heidepiek/Retro_Clock_2/Images/Back_of_Rear_Cover.jpg

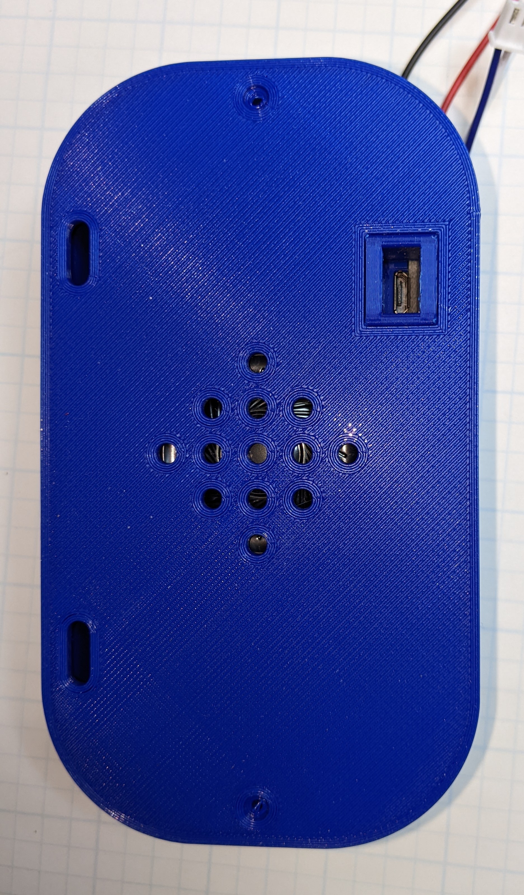
Images/Back_of_Rear_Cover.jpg
