heidepiek/Retro_Clock_2/Images/Bezel&Decal.jpg

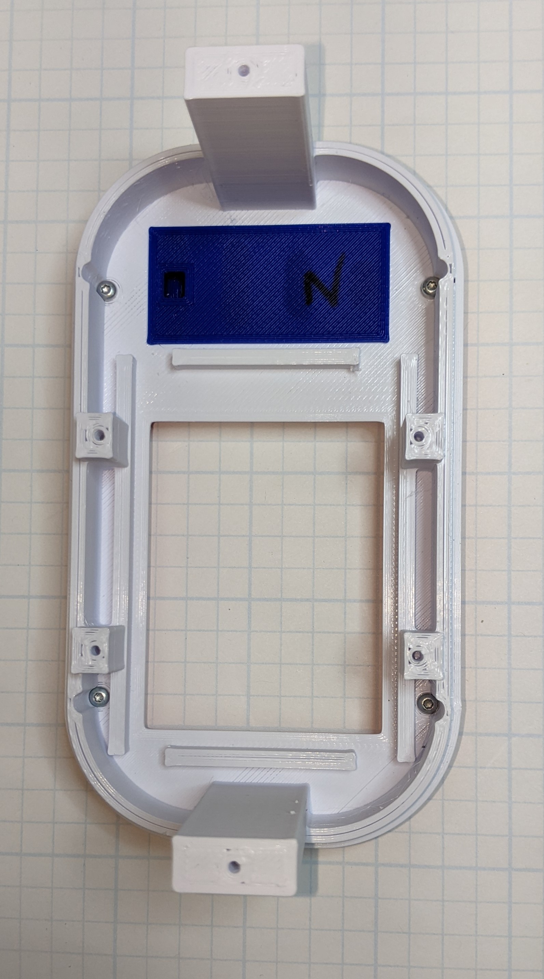
Images/Bezel&Decal.jpg
