heidepiek/Retro_Clock_2/Images/Bezel.jpg

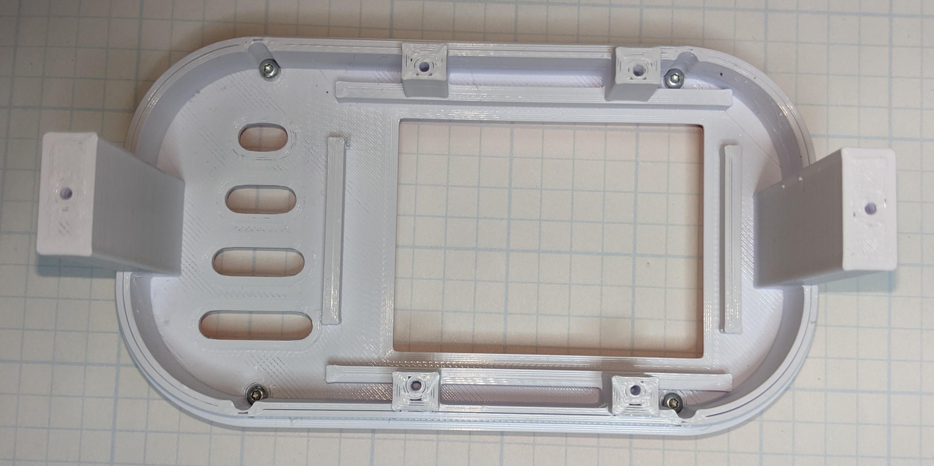
Images/Bezel.jpg
