heidepiek/Retro_Clock_2/Images/Bezel_&_Trim.jpg

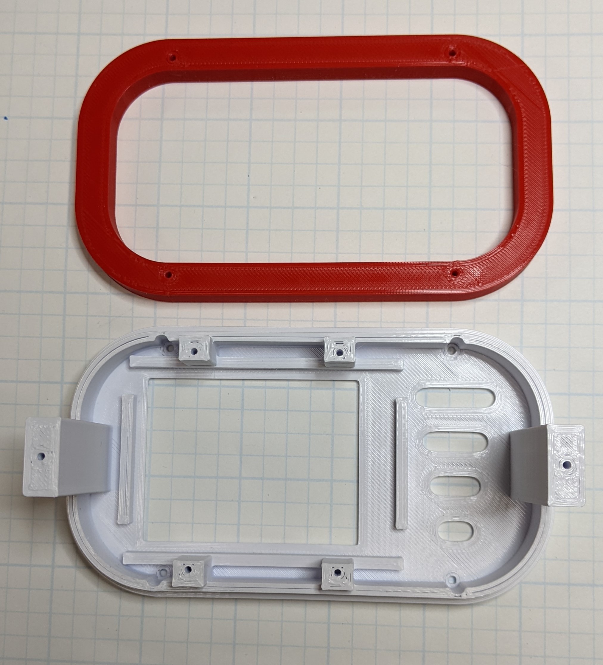
Images/Bezel_&_Trim.jpg
