heidepiek/Retro_Clock_2/Images/Bezel_Assy_&_Rear_Cover.jpg

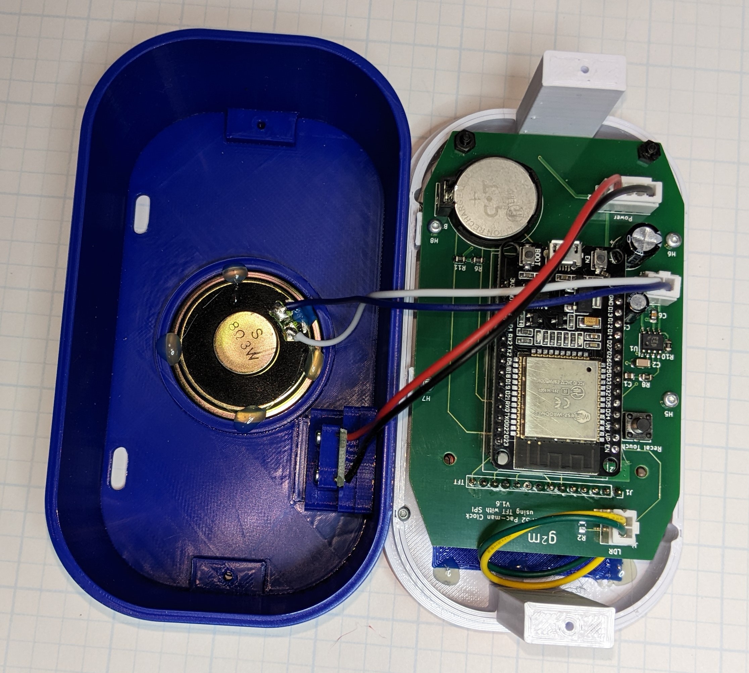
Images/Bezel_Assy_&_Rear_Cover.jpg
