heidepiek/Retro_Clock_2/Images/Bezel_with PCB_Assy.jpg

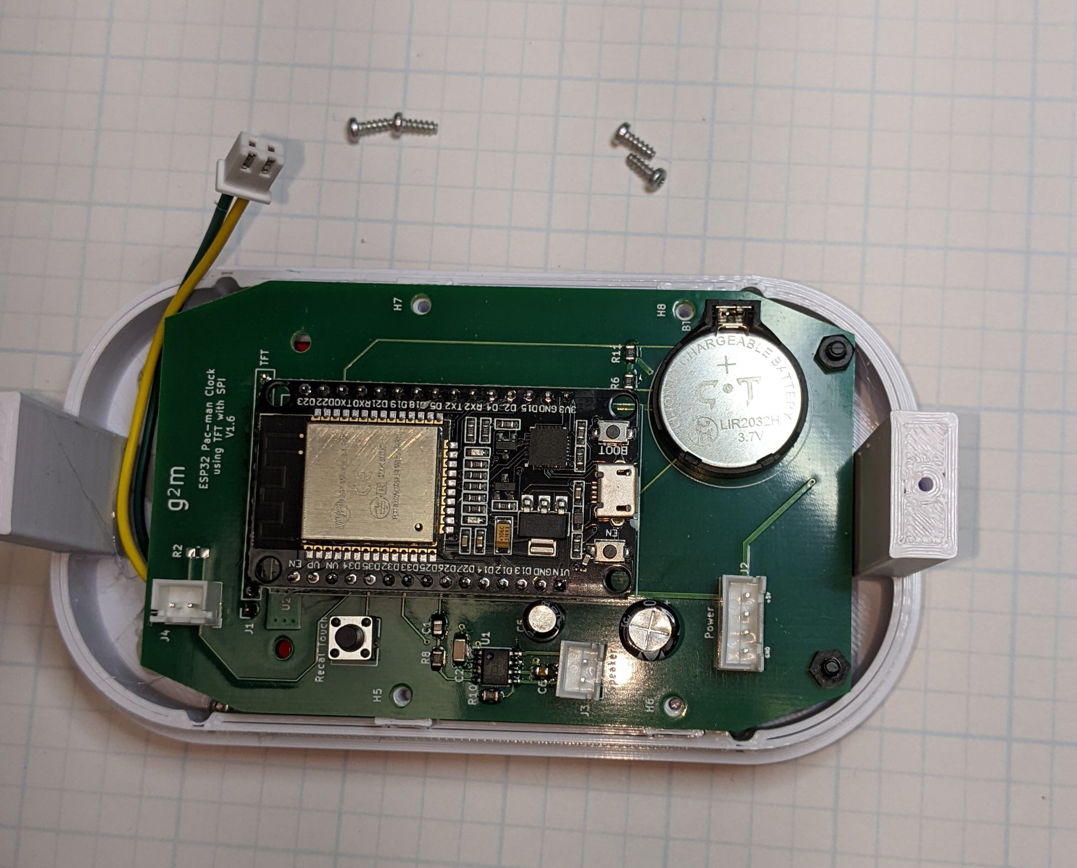
Images/Bezel_with PCB_Assy.jpg
