heidepiek/Retro_Clock_2/Images/Bezel_with_PCB_2.jpg

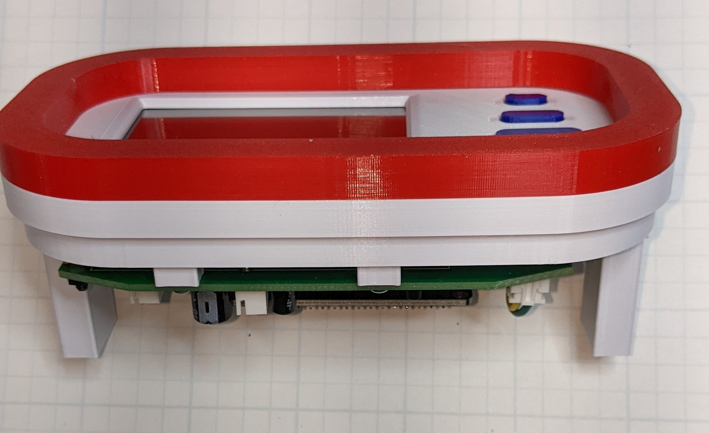
Images/Bezel_with_PCB_2.jpg
