heidepiek/Retro_Clock_2/Images/Decal&Bezel_Hotglue.jpg

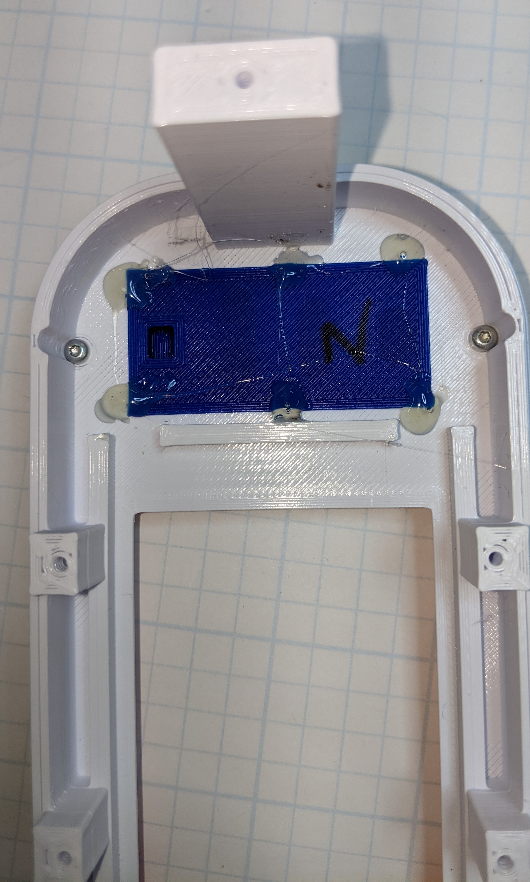
Images/Decal&Bezel_Hotglue.jpg
