heidepiek/Retro_Clock_2/Images/Decal.jpg

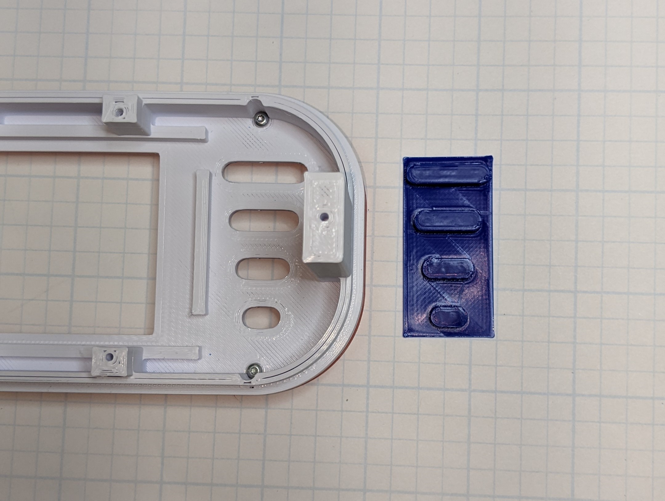
Images/Decal.jpg
