heidepiek/Retro_Clock_2/Images/Decal_with_LDR.jpg

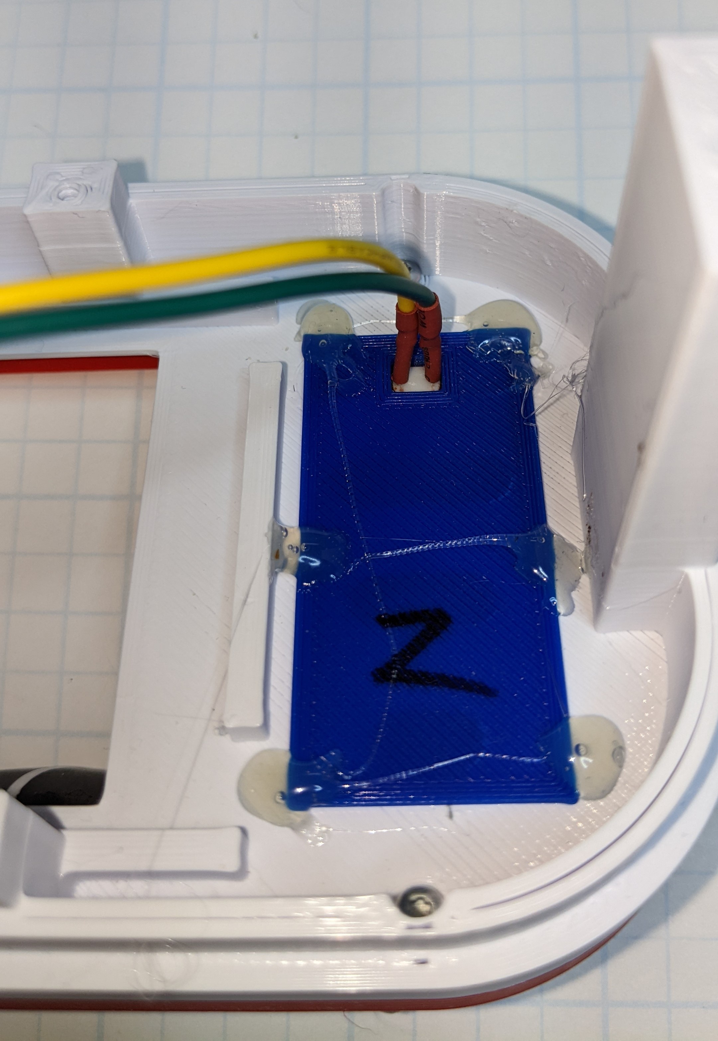
Images/Decal_with_LDR.jpg
