heidepiek/Retro_Clock_2/Images/LDR_Assy.jpg

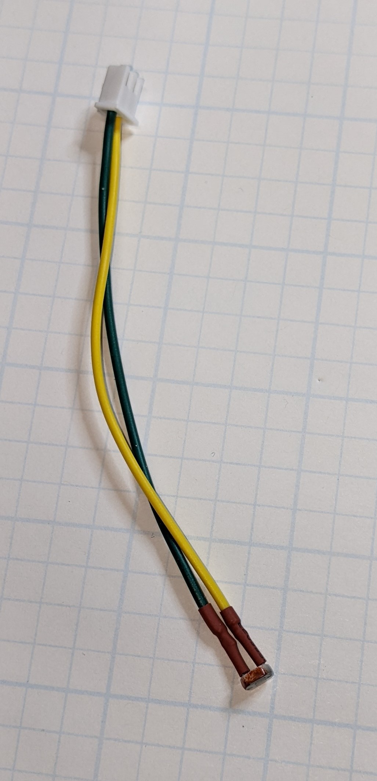
Images/LDR_Assy.jpg
