heidepiek/Retro_Clock_2/Images/LDR_Connected_to_PCB_Assy.jpg

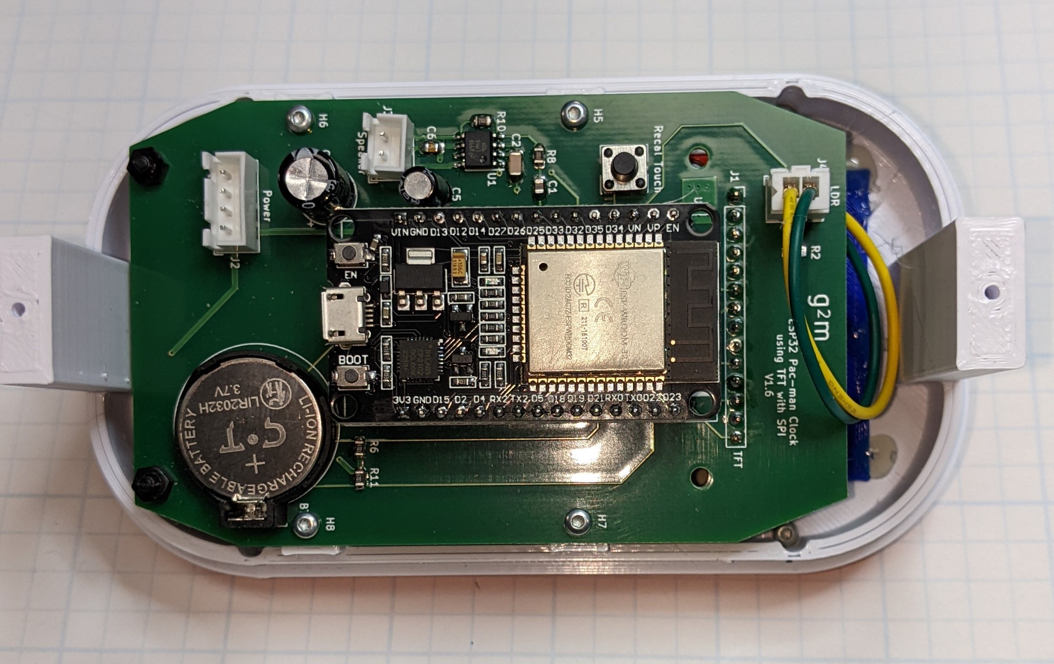
Images/LDR_Connected_to_PCB_Assy.jpg
