heidepiek/Retro_Clock_2/Images/LDR_Hotglued.jpg

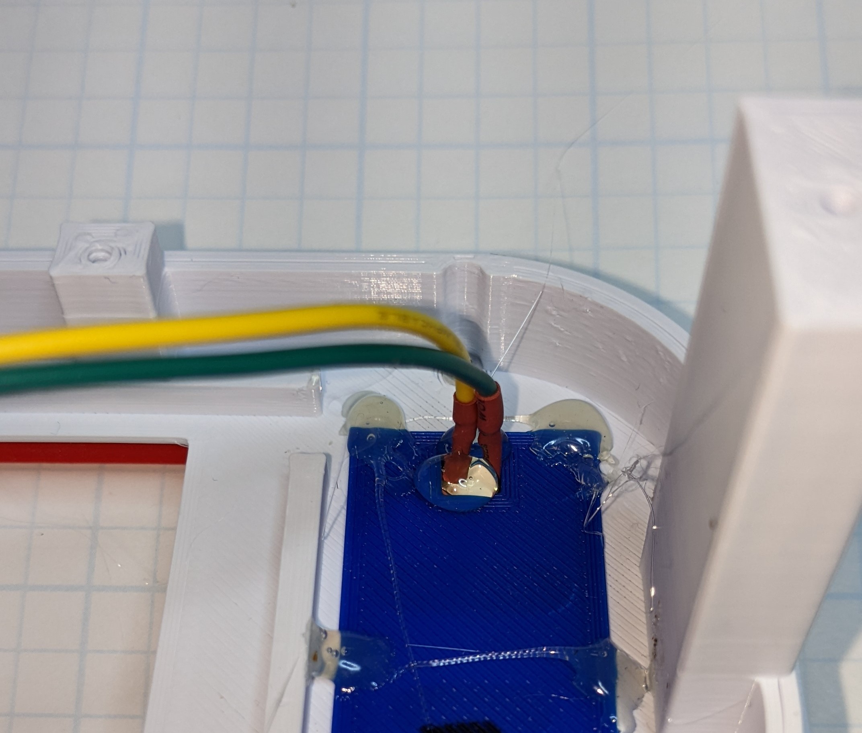
Images/LDR_Hotglued.jpg
