heidepiek/Retro_Clock_2/Images/PCB_&_Processor.jpg

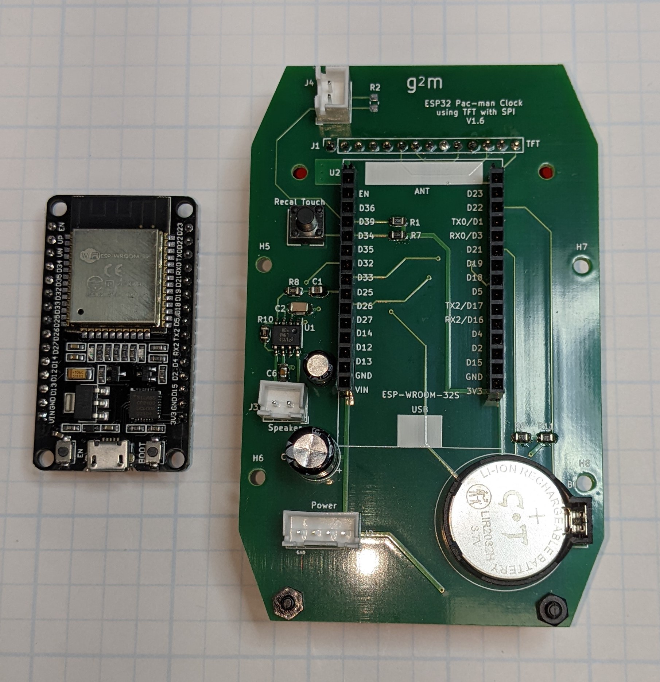
Images/PCB_&_Processor.jpg
