heidepiek/Retro_Clock_2/Images/PCB_Assy_Mounted_in_Bezel.jpg

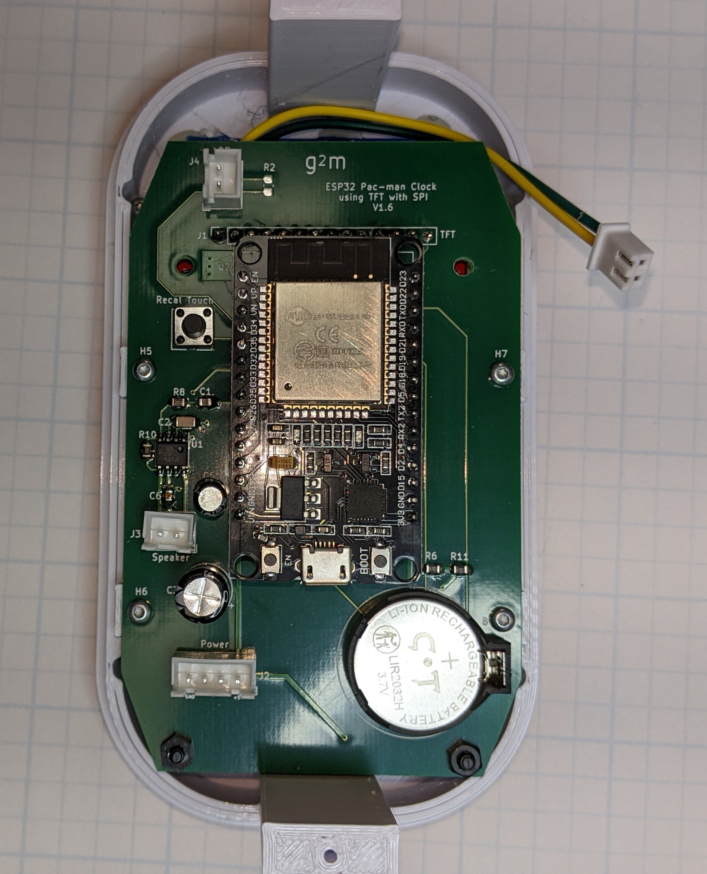
Images/PCB_Assy_Mounted_in_Bezel.jpg
