heidepiek/Retro_Clock_2/Images/PCB_Bottom.jpg

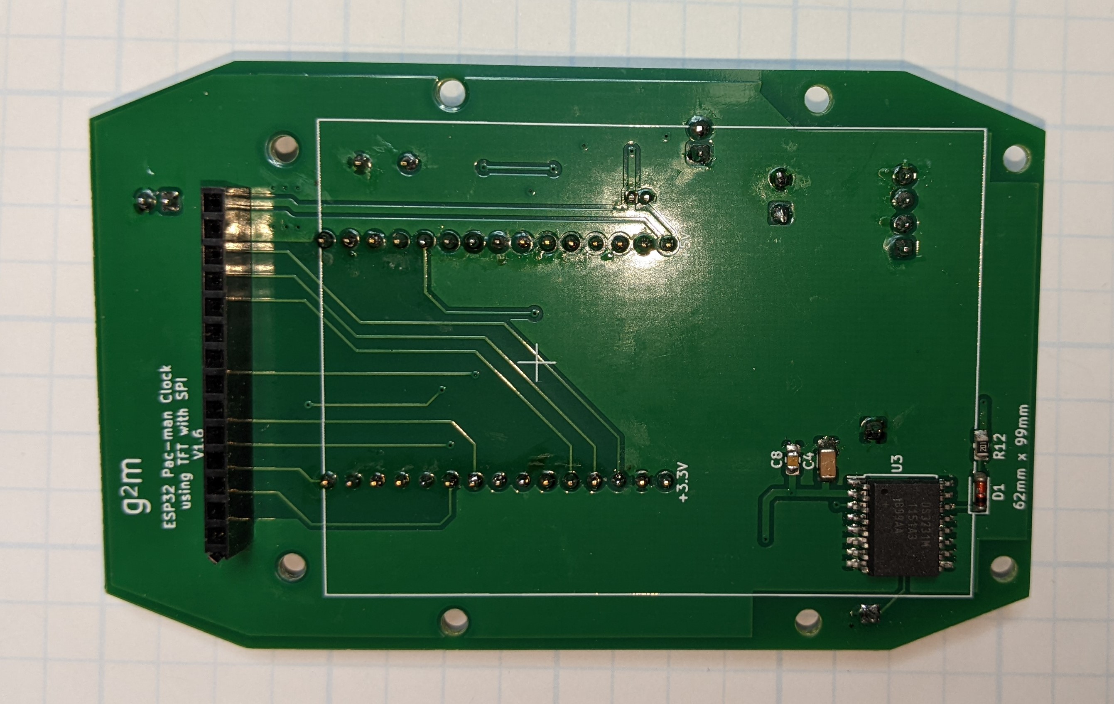
Images/PCB_Bottom.jpg
