heidepiek/Retro_Clock_2/Images/PCB_Top.jpg

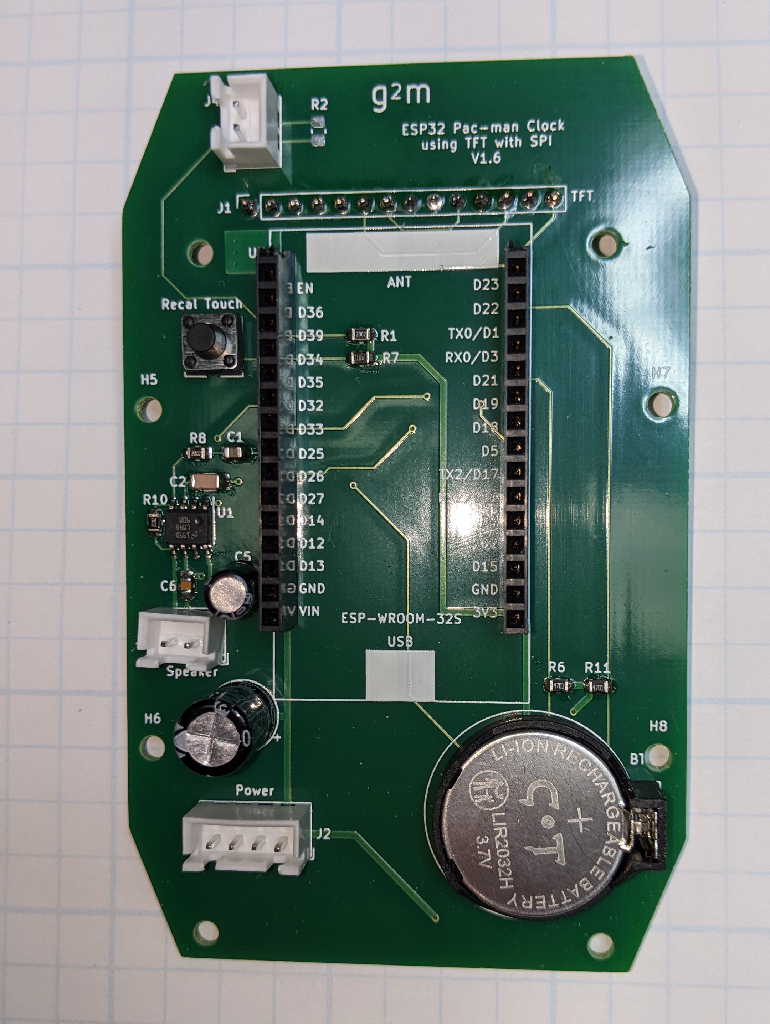
Images/PCB_Top.jpg
