heidepiek/Retro_Clock_2/Images/PCB_with_Processor.jpg

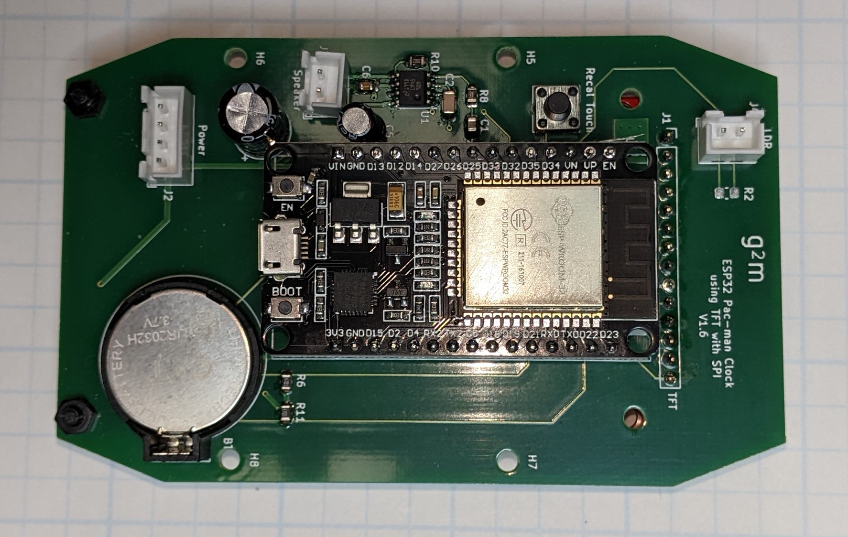
Images/PCB_with_Processor.jpg
