heidepiek/Retro_Clock_2/Images/Rear_Cover_&_USB_Assy.jpg

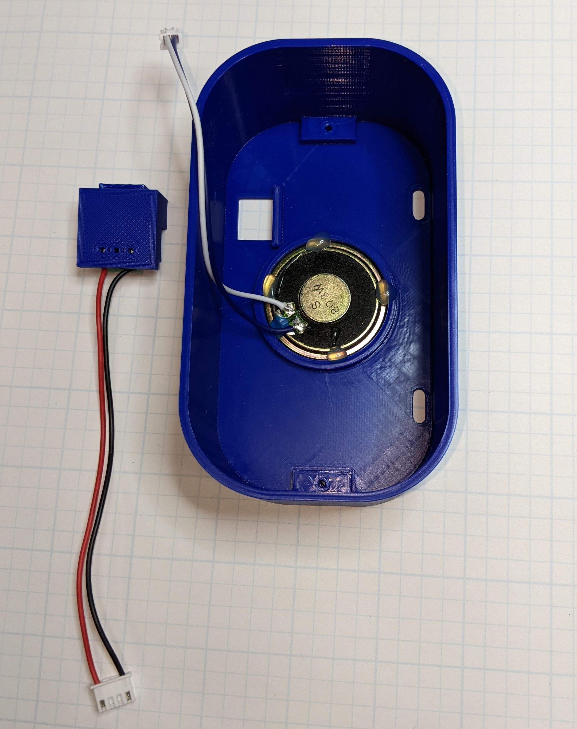
Images/Rear_Cover_&_USB_Assy.jpg
