heidepiek/Retro_Clock_2/Images/Rear_Cover_Screws.jpg

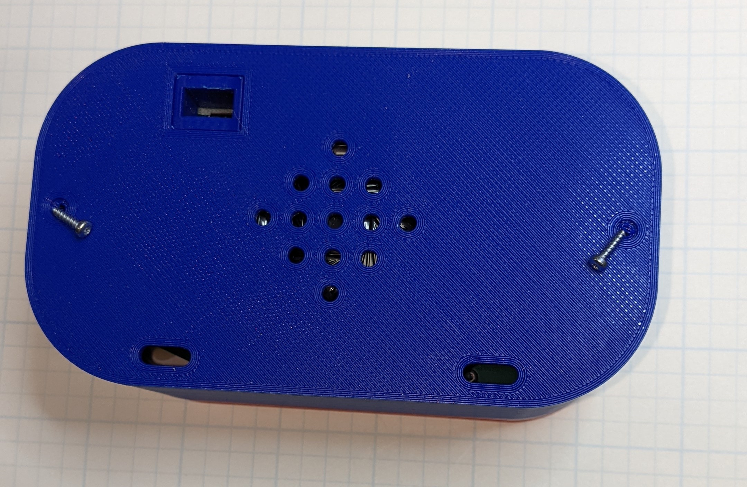
Images/Rear_Cover_Screws.jpg
