heidepiek/Retro_Clock_2/Images/RearCover & Speaker.jpg

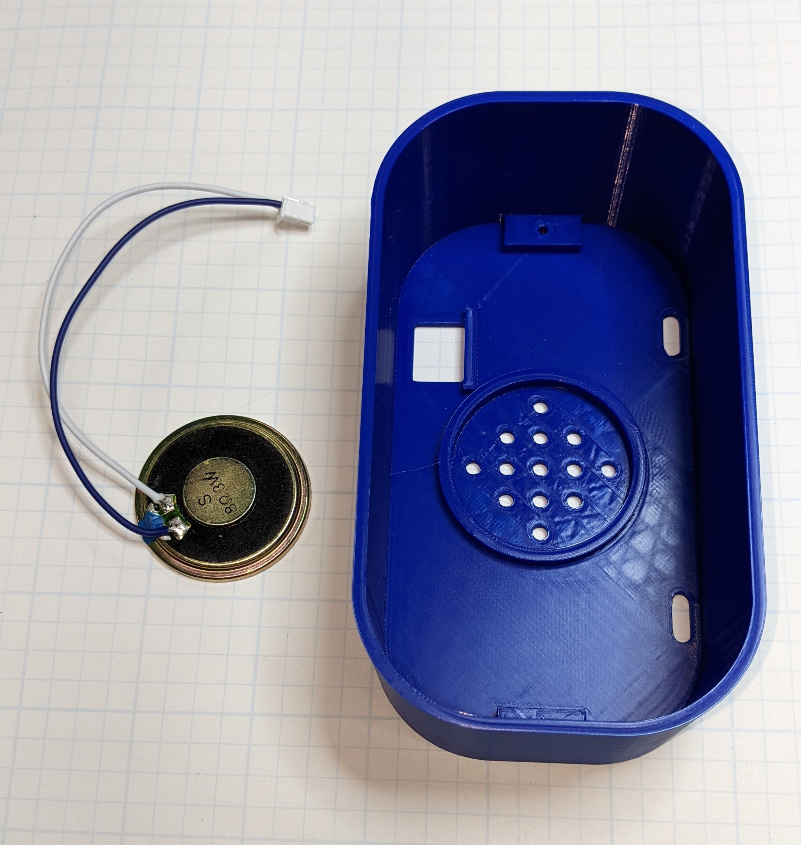
Images/RearCover & Speaker.jpg
