heidepiek/Retro_Clock_2/Images/Retro_Clock_Face.jpg

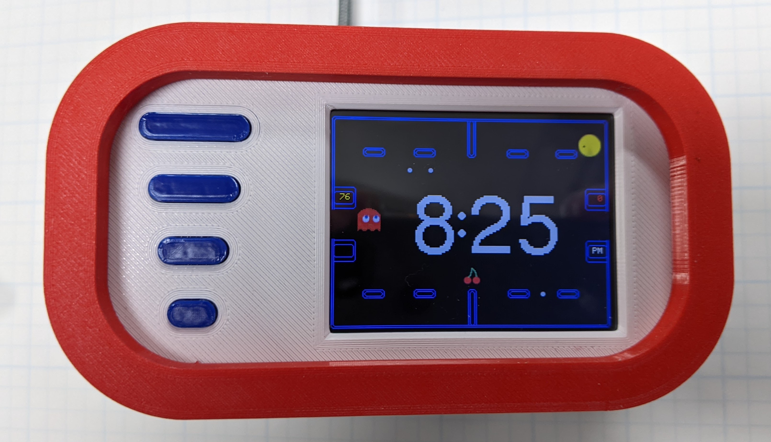
Images/Retro_Clock_Face.jpg
