heidepiek/Retro_Clock_2/Images/Speaker.jpg

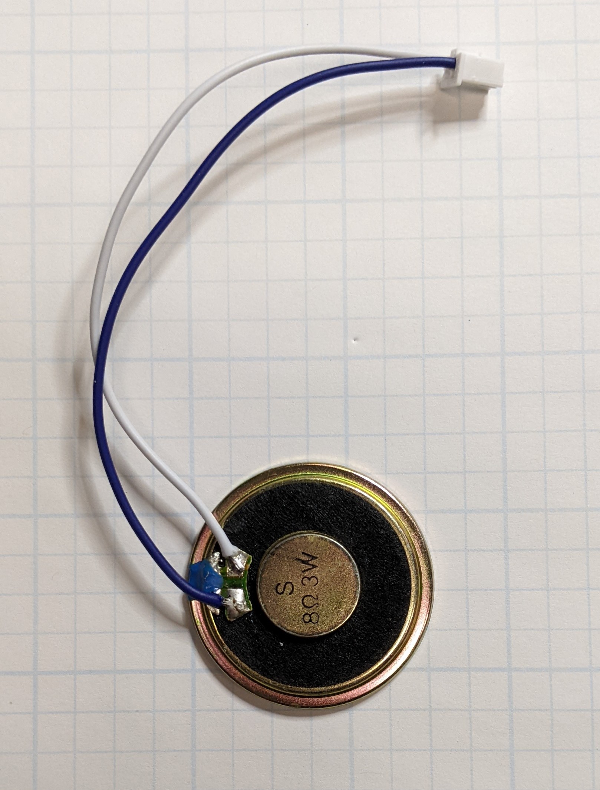
Images/Speaker.jpg
