heidepiek/Retro_Clock_2/Images/Speaker_Hotglued.jpg

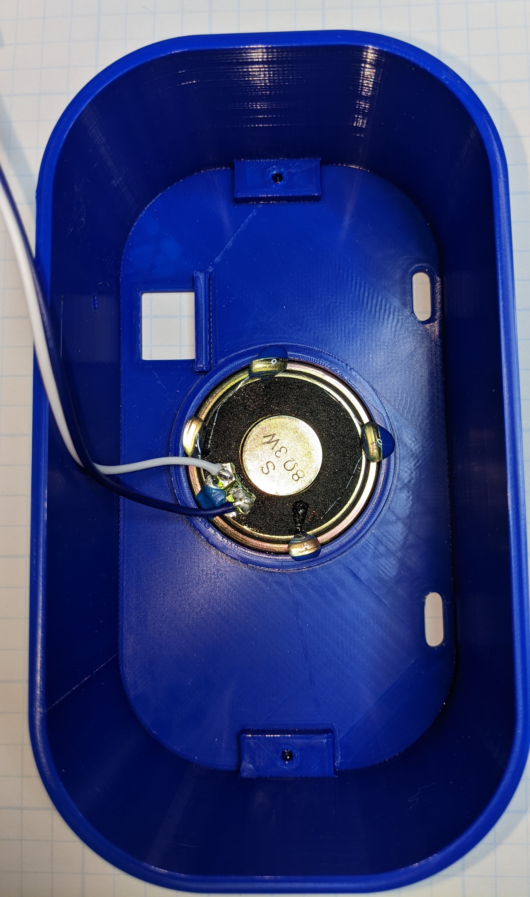
Images/Speaker_Hotglued.jpg
