heidepiek/Retro_Clock_2/Images/Speaker_in_Rear_Cover.jpg

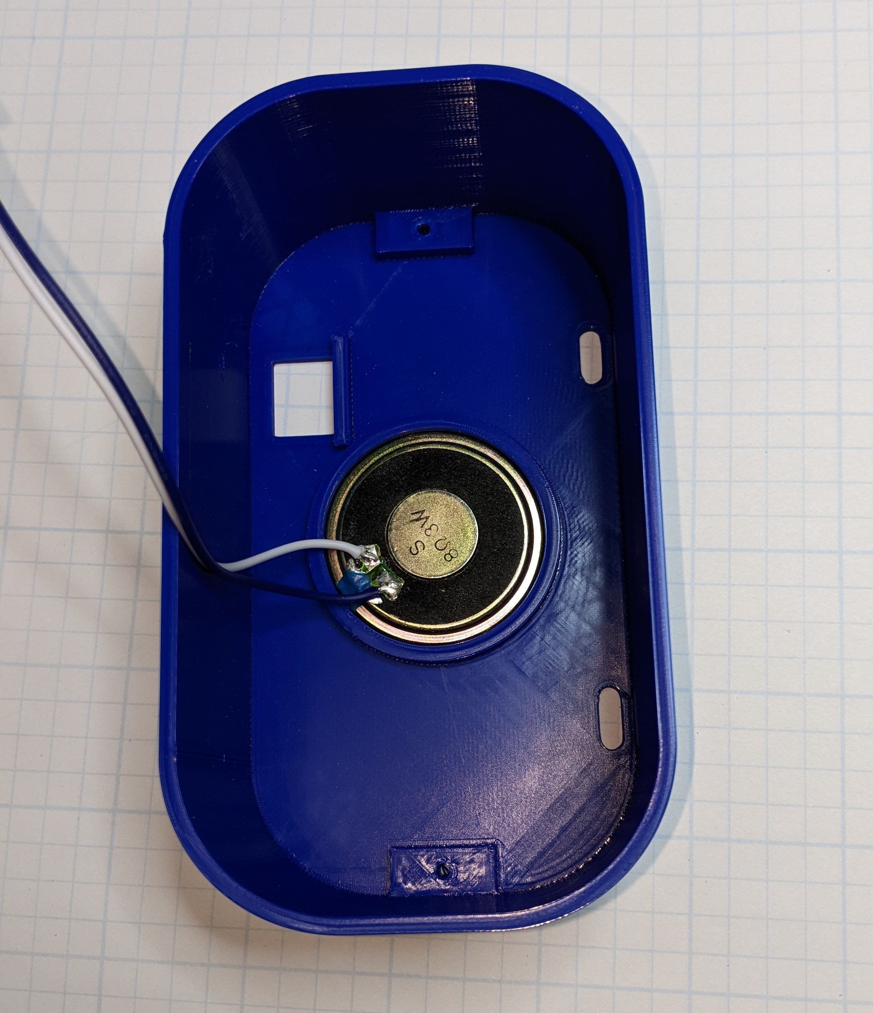
Images/Speaker_in_Rear_Cover.jpg
