heidepiek/Retro_Clock_2/Images/TFT_with_Standoffs.jpg

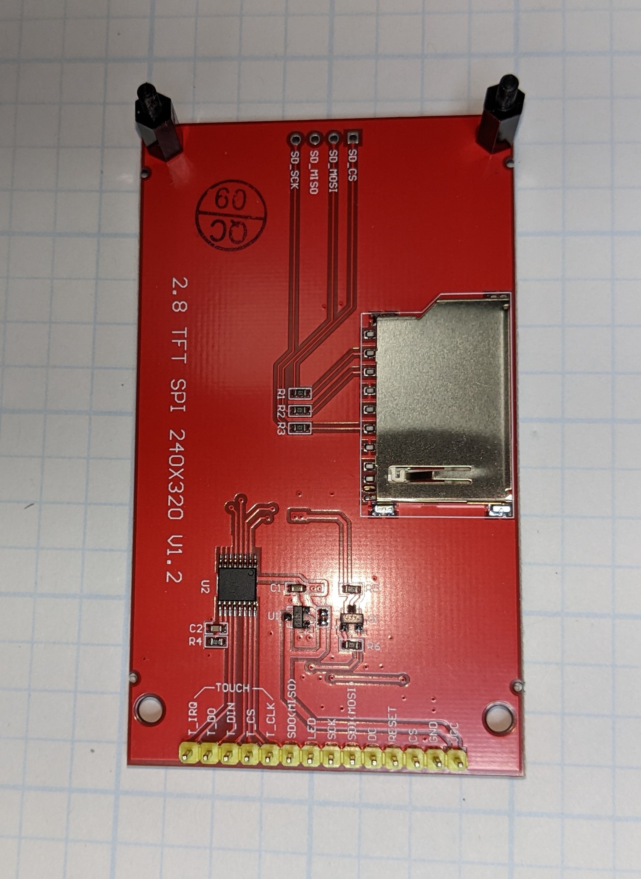
Images/TFT_with_Standoffs.jpg
