heidepiek/Retro_Clock_2/Images/USB_Bracket.jpg

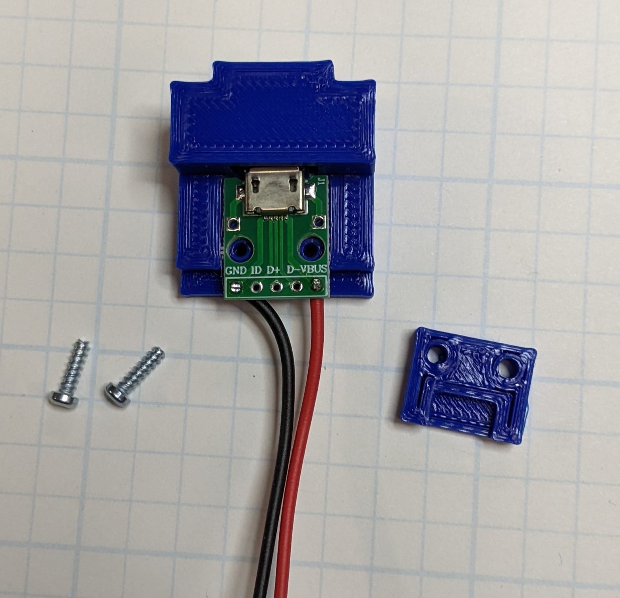
Images/USB_Bracket.jpg
