heidepiek/Retro_Clock_2/Images/USB_Bracket_Assy.jpg

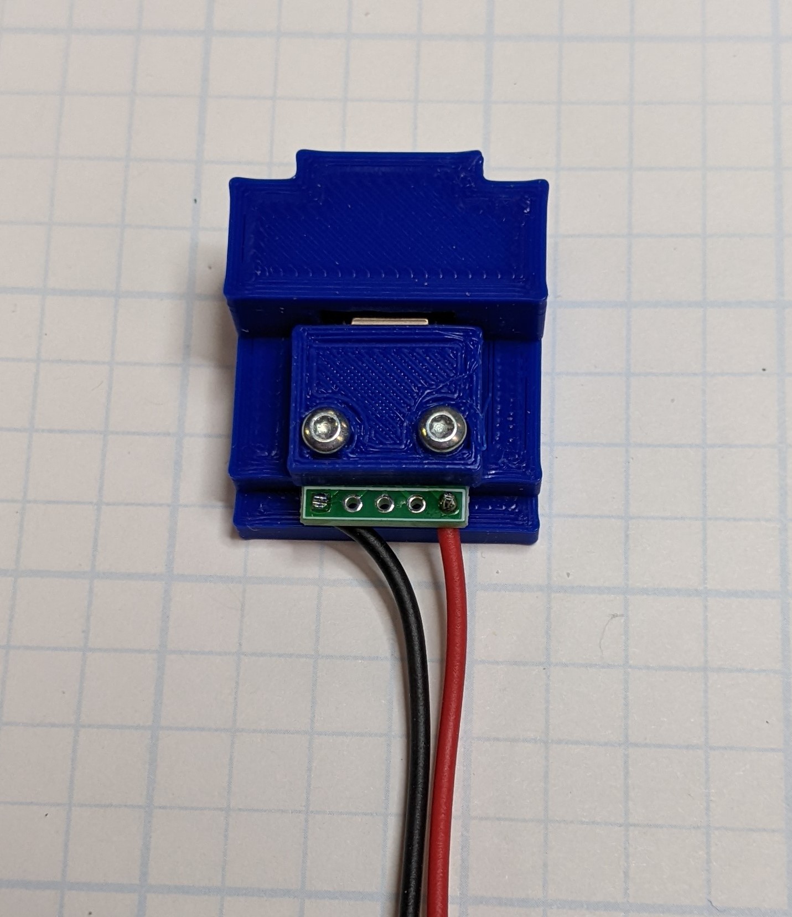
Images/USB_Bracket_Assy.jpg
