heidepiek/Retro_Clock_2/Images/USB_Securred.jpg

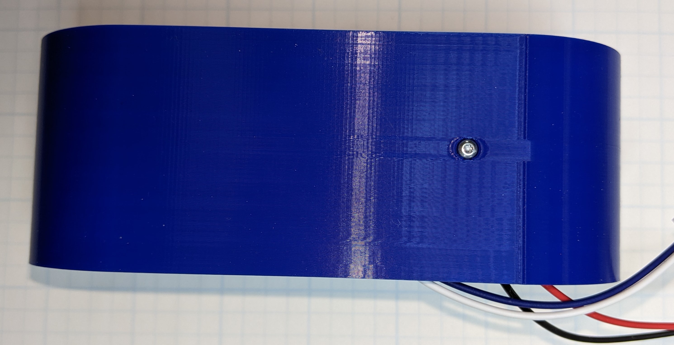
Images/USB_Securred.jpg
