heidepiek/Retro_Clock_2/Images/Assembled_Bezel&Trim.jpg

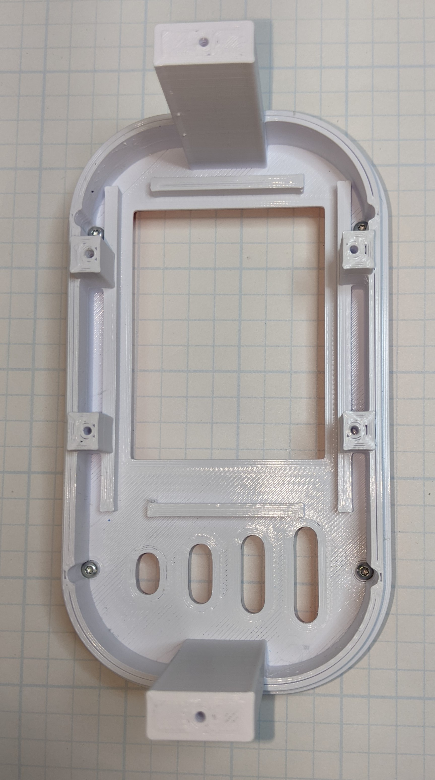
Images/Assembled_Bezel&Trim.jpg
