heidepiek/Retro_Clock_2/Images/Clock_with_Feet_Installed.jpg

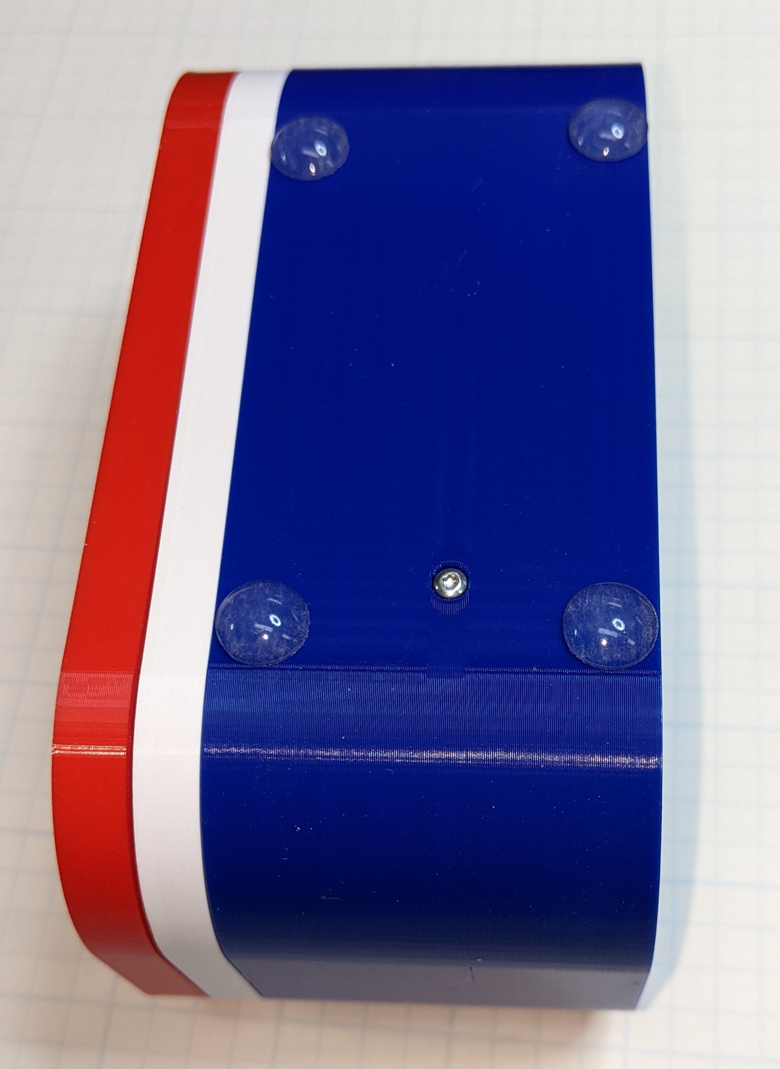
Images/Clock_with_Feet_Installed.jpg
