heidepiek/Retro_Clock_2/Images/PCB_TFT_Assembly.jpg

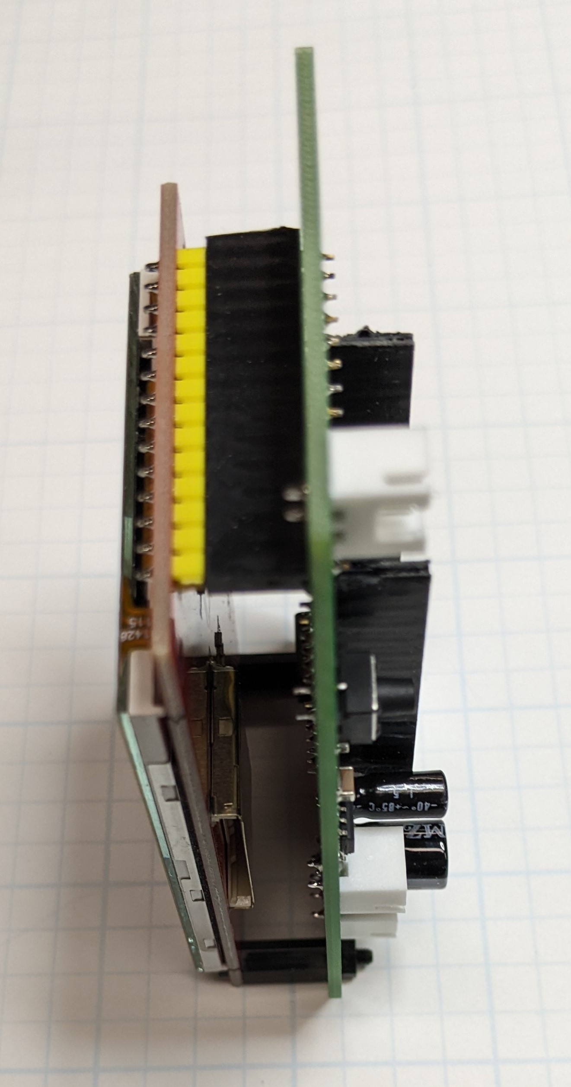
Images/PCB_TFT_Assembly.jpg
