heidepiek/Retro_Clock_2/Images/Rear_Cover_with_USB_Installed.jpg

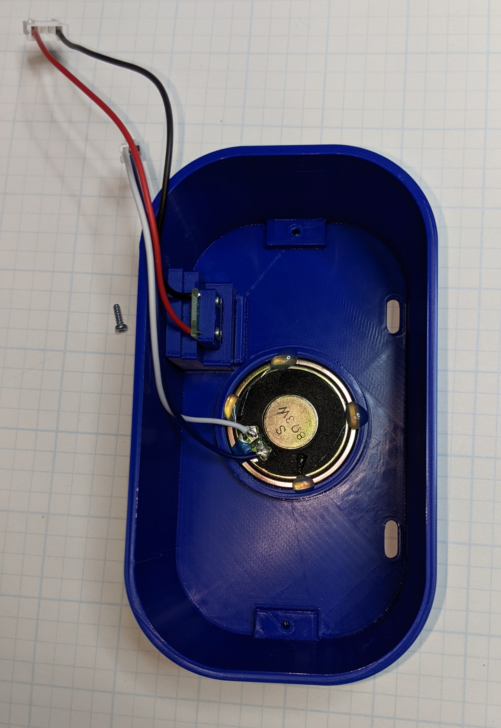
Images/Rear_Cover_with_USB_Installed.jpg
