heidepiek/Retro_Clock_2/src/SoundData.h

// sound in WAV format, we're not concerned with most of the header bytes
// just samples per second and data size, we will always save in 8bit 
// unsigned pcm
// sample rate is at offset 24 (4 bytes), data size at offset 4 (4bytes)
//
//  PlayingTime = 4307.5 milliseconds (approx 4.3 seconds)

#ifdef BUFFERED_WAV
//
//  When using BUFFERED_WAV, the pacman and gobble WAV data occupy the same buffer
//  to save on memory. The pacman WAV starts at offset 0 and the gobble WAV starts 
//  at offset 48 so that both the pacman and gobble WAV headers are in memory when 
//  the Pacman and pacmangobble objects are created.
//  Whenever a request is made to play either WAV the code knows
//  which WAV is occupying the buffer and if not the requested WAV it will
//  load the desired WAV from SPIFFS. 
//  The gobble WAV is about half the size of the pacman WAV.
//
//  size = 34468
//
unsigned char PROGMEM PM[35000] = {
  //  pacman WAV header
  0x52, 0x49, 0x46, 0x46, 0x9C, 0x86, 0x00, 0x00, 0x57, 0x41, 0x56, 0x45,   // size[7:4} = 0x0000869C (34460)
  0x66, 0x6D, 0x74, 0x20, 0x10, 0x00, 0x00, 0x00, 0x01, 0x00, 0x01, 0x00,   // FMT chunk ID[15:12] = 0x20746D66
  0x40, 0x1F, 0x00, 0x00, 0x40, 0x1F, 0x00, 0x00, 0x01, 0x00, 0x08, 0x00,   // sample rate[27:24] 0x00001F40 (8000)
  0x64, 0x61, 0x74, 0x61, 0x13, 0x86, 0x00, 0x00, 0x80, 0x7F, 0x7F, 0x7F,   // Data start
  // gobble WAV header
  0x52, 0x49, 0x46, 0x46, 0x5A, 0x3E, 0x00, 0x00, 0x57, 0x41, 0x56, 0x45,   // size[7:4] = 0x00003E5A (15962)
  0x66, 0x6D, 0x74, 0x20, 0x10, 0x00, 0x00, 0x00, 0x01, 0x00, 0x01, 0x00,   // FMT chunk ID[15:12] = 0x20746D66
  0x22, 0x56, 0x00, 0x00, 0x22, 0x56, 0x00, 0x00, 0x01, 0x00, 0x08, 0x00,   // sample rate[27:24] = 0x00005622 (22050)
  0x64, 0x61, 0x74, 0x61, 0xB8, 0x3D, 0x00, 0x00, 0x81, 0x82, 0x80, 0x80,   // Data start
};

#else
unsigned char PROGMEM PM[34468] = {
  0x52, 0x49, 0x46, 0x46, 0x9C, 0x86, 0x00, 0x00, 0x57, 0x41, 0x56, 0x45,   // size[7:4} = 0x0000869C (34460)
  0x66, 0x6D, 0x74, 0x20, 0x10, 0x00, 0x00, 0x00, 0x01, 0x00, 0x01, 0x00,   // FMT chunk ID[15:12] = 0x20746D66
  0x40, 0x1F, 0x00, 0x00, 0x40, 0x1F, 0x00, 0x00, 0x01, 0x00, 0x08, 0x00,   // sample rate[27:24] 0x00001F40 (8000)
  0x64, 0x61, 0x74, 0x61, 0x13, 0x86, 0x00, 0x00, 0x80, 0x7F, 0x7F, 0x7F,   // Data start 
  0x7F, 0x7F, 0x7F, 0x7F, 0x7F, 0x7F, 0x7F, 0x7F, 0x7F, 0x7F, 0x7F, 0x7F,
  0x7F, 0x7F, 0x7F, 0x7F, 0x7F, 0x7F, 0x7F, 0x7F, 0x7F, 0x7F, 0x7F, 0x7F,
  0x7F, 0x7F, 0x7F, 0x7F, 0x7F, 0x7F, 0x7F, 0x7F, 0x7F, 0x7F, 0x7F, 0x7F,
  0x7F, 0x7F, 0x7F, 0x7F, 0x7F, 0x7F, 0x7F, 0x7F, 0x7F, 0x7F, 0x7F, 0x7F,
  0x7F, 0x7F, 0x7F, 0x7F, 0x7F, 0x7F, 0x7F, 0x7F, 0x7F, 0x7F, 0x7F, 0x7F,
  0x7F, 0x7F, 0x7F, 0x7F, 0x7F, 0x7F, 0x7F, 0x7F, 0x80, 0x7F, 0x7F, 0x7F,
  0x7F, 0x7F, 0x7F, 0x7F, 0x7F, 0x7F, 0x7F, 0x80, 0x7F, 0x7F, 0x7F, 0x7F,
  0x7F, 0x7F, 0x7F, 0x7F, 0x7F, 0x7F, 0x7F, 0x7F, 0x7F, 0x7F, 0x7F, 0x7F,
  0x7F, 0x7F, 0x7F, 0x7F, 0x7F, 0x7F, 0x7F, 0x7F, 0x7F, 0x7F, 0x7F, 0x7F,
  0x7F, 0x7F, 0x7F, 0x7F, 0x7F, 0x7F, 0x7F, 0x7F, 0x7F, 0x7F, 0x7F, 0x7F,
  0x7F, 0x7F, 0x7F, 0x7F, 0x7F, 0x7F, 0x7F, 0x7F, 0x7F, 0x7F, 0x7F, 0x7F,
  0x7F, 0x7F, 0x7F, 0x7F, 0x7F, 0x7F, 0x7F, 0x7F, 0x7F, 0x7F, 0x7F, 0x7F,
  0x80, 0x7F, 0x7F, 0x7F, 0x7F, 0x7F, 0x7F, 0x7F, 0x7F, 0x7F, 0x7F, 0x7F,
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
  0x8C, 0x8E, 0x8D, 0x8E, 0x8D, 0x8E, 0x8D, 0x8B, 0x8B, 0x89, 0x86, 0x84,
  0x7F, 0x7D, 0x78, 0x76, 0x75, 0x72, 0x71, 0x70, 0x6F, 0x70, 0x6E, 0x6E,
  0x6D, 0x6F, 0x70, 0x71, 0x71, 0x72, 0x70, 0x71, 0x70, 0x71, 0x71, 0x74,
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
};
#endif      //#ifdef BUFFERED_WAV
